icebreaker-ch/OpenSPortSensor/images/ExampleConfiguration.kicad_sch

## KiCad design images/ExampleConfiguration.kicad_sch (2024-02-15)

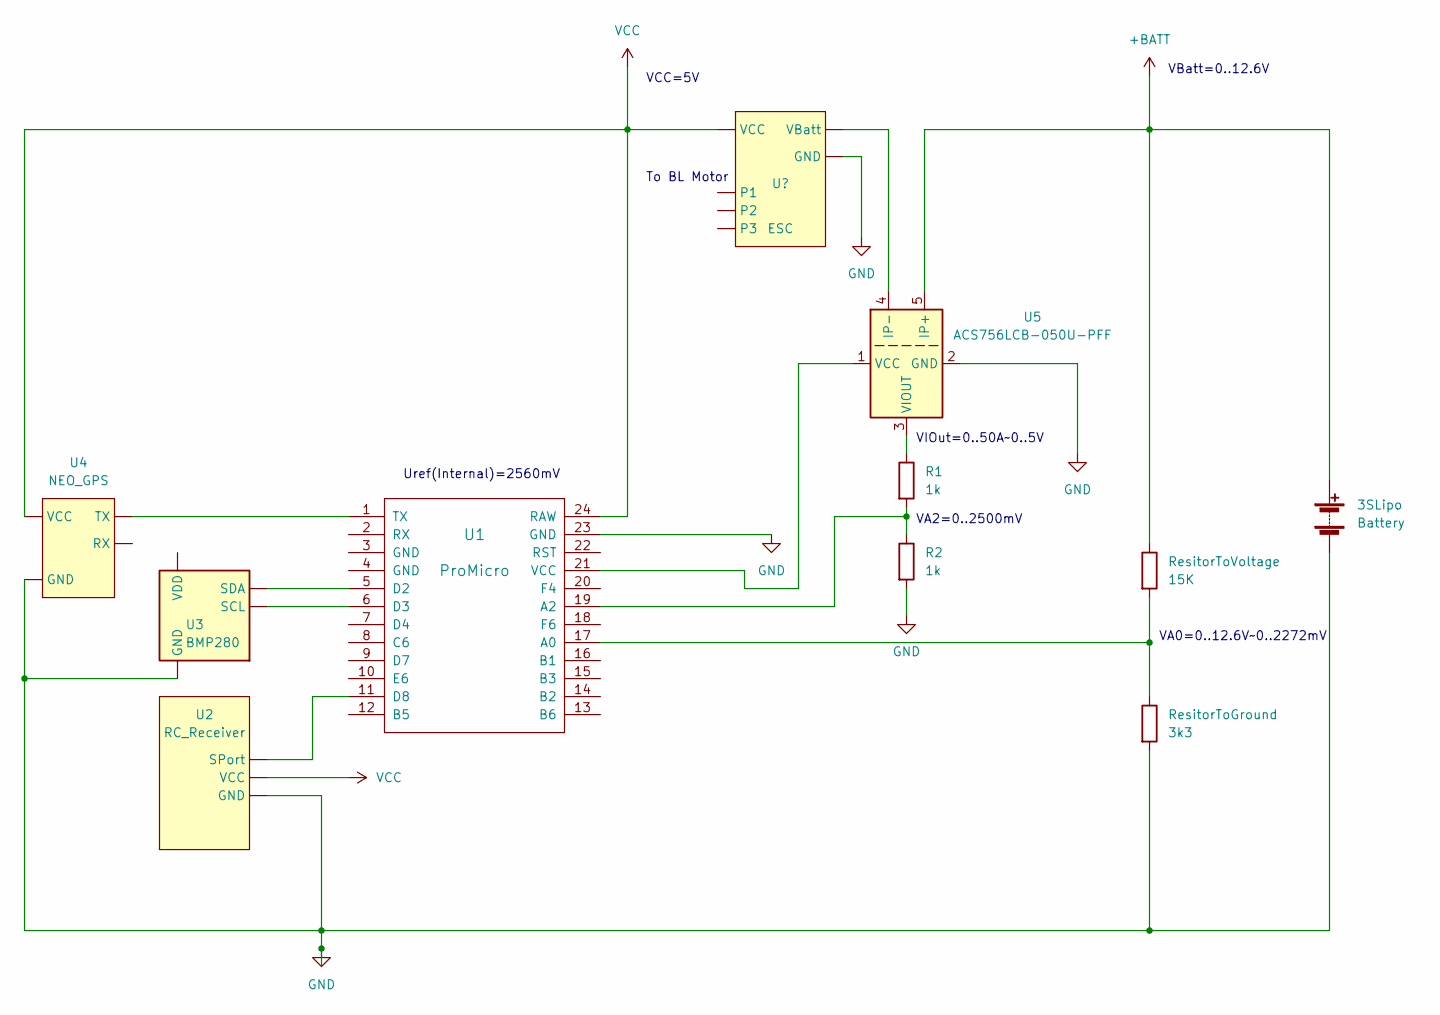
[picture p9: schematic ExampleConfiguration.kicad_sch]

Parts:
3SLipo: Battery
R1, R2: 1k
ResitorToGround: 3k3
ResitorToVoltage: 15K
U1: ProMicro
U2: RC_Receiver
U3: BMP280; Bosch_LGA-8_2x2.5mm_P0.65mm_ClockwisePinNumbering
U4: NEO_GPS
U5: ACS756LCB-050U-PFF; Allegro_CB_PFF

Connections:
unnamed: 3SLipo.1 (+), ResitorToVoltage.1, U5.5 (IP-)
unnamed: 3SLipo.2 (-), ResitorToGround.2, U2., U3., U4.
unnamed: R1.1, U5.3 (VIOUT)
unnamed: R1.2, R2.1, U1.19 (F5)
unnamed: ResitorToGround.1, ResitorToVoltage.2, U1.17 (F7)
unnamed: U1.1 (TX), U4.
unnamed: U1.5 (SDA), U3.
unnamed: U1.6 (SCL), U3.
unnamed: U1.11 (B4), U2.
unnamed: U1.21 (VCC), U5.1 (VCC)
unnamed: U1.24 (RAW), U4.

Notes on the sheet:
VCC=5V
VA0=0..12.6V~0..2272mV
VA2=0..2500mV
VBatt=0..12.6V
To BL Motor
Uref(Internal)=2560mV
VIOut=0..50A~0..5V
