icebreaker-ch/OpenSPortSensor/src/Filter.h

#ifndef FILTER_H
#define FILTER_H

/**
 * Abstract class for filtering values by any algorithm.
*/
class Filter {
    public:
        virtual void reset() = 0;
        virtual void addValue(float newValue) = 0;
        virtual unsigned int getNumValues() = 0;
        virtual float getFilteredValue() = 0;
        virtual ~Filter() = 0;
};

#endif
